AkhileshGowrishetty/GPS-Tracker/assets/images/image2.jpeg

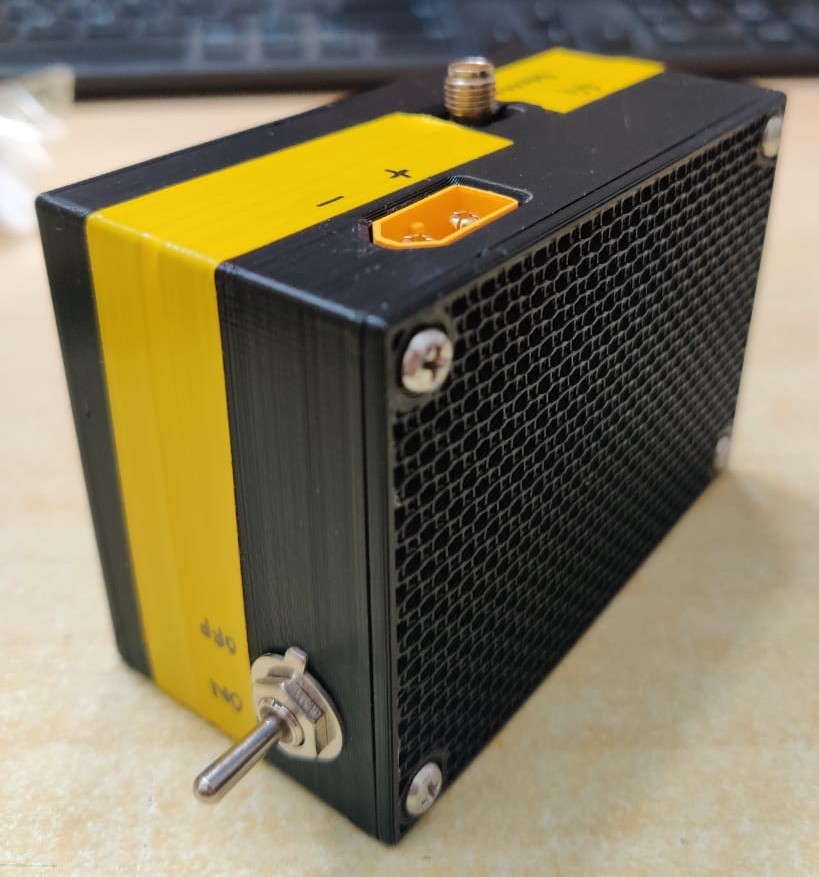
assets/images/image2.jpeg
